2Radu2/Nemesis/Images/Final Stack/side view.jpeg

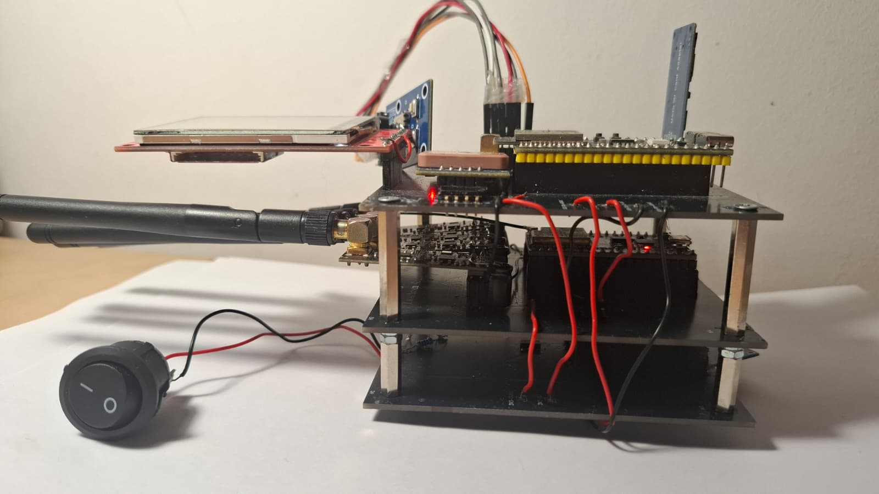
Images/Final Stack/side view.jpeg
