2Radu2/Nemesis/Images/PCB populated & unpopulated/bt jammer pop.jpeg

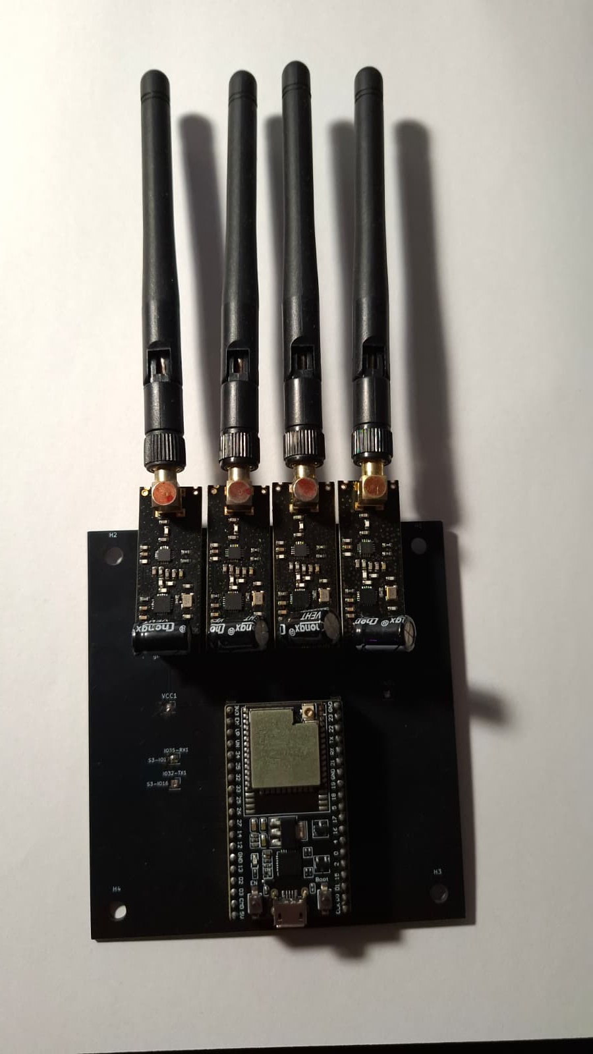
Images/PCB populated & unpopulated/bt jammer pop.jpeg
