2Radu2/Nemesis/Images/PCB populated & unpopulated/esp8266 pop.jpeg

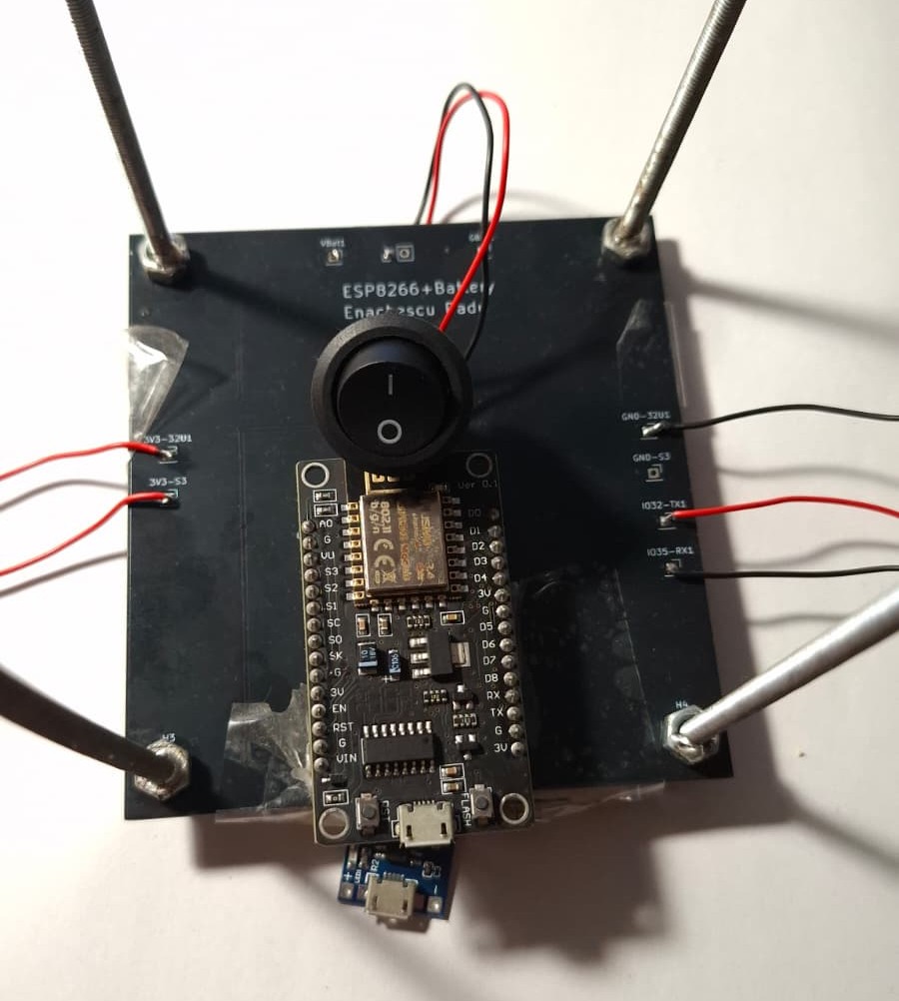
Images/PCB populated & unpopulated/esp8266 pop.jpeg
