2Radu2/Nemesis/Images/User Interface/bt interface.jpeg

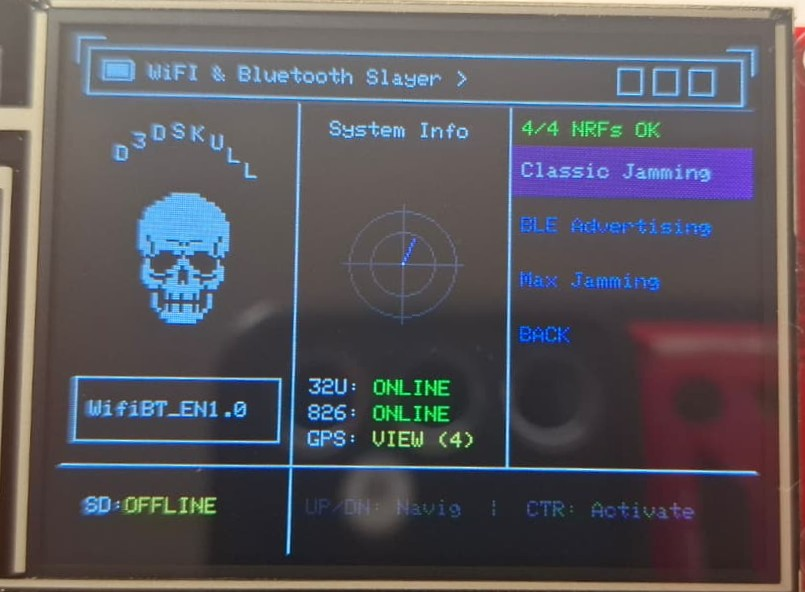
Images/User Interface/bt interface.jpeg
