2Radu2/Nemesis/Images/User Interface/initial interface.jpeg

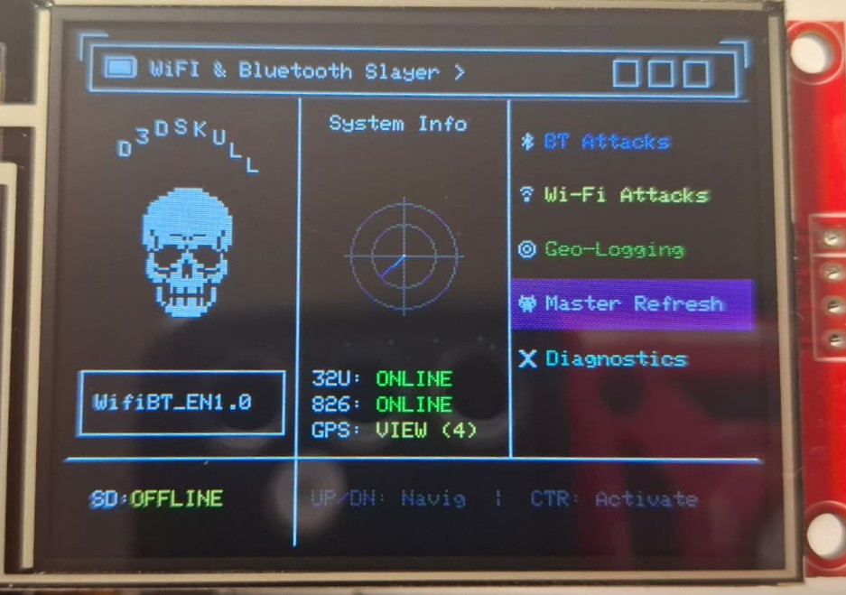
Images/User Interface/initial interface.jpeg
