2Radu2/Nemesis/Images/User Interface/wifi interface.jpeg

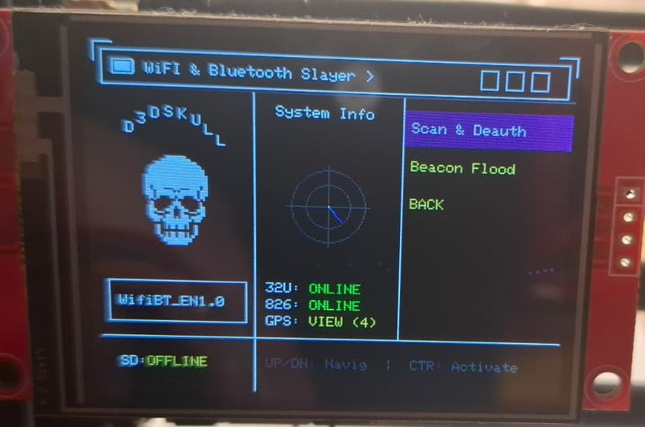
Images/User Interface/wifi interface.jpeg
